henjin0/Kari-Kuruma/imagefile/cut.jpg

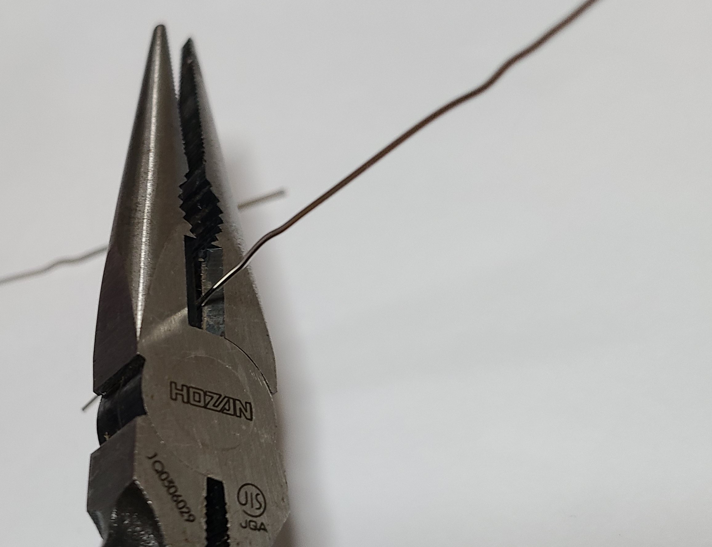
imagefile/cut.jpg
